Volus208/BioMeta/pcb/pcb.kicad_sch

## KiCad design pcb/pcb.kicad_sch (2023-11-06)

Schematic: pcb.kicad_sch

Parts:
D1, D2, D3, D4, D5, D6, D7, D8, D9, D10, D11, D12, D13, D14, D15, D16, D17, D18, D19, D20, D21, D22, D23, D24, D25, D26, D27, D28, D29, D30, D31, D32, D33, D34, D35, D36, D37, D38, D39, D40, D41, D42, D43, D44, D45, D46, D47, D48, D49, D50, D51, D52, D53, D54, D55, D56, D57, D58, D59, D60, D61, D62, D63, D64, D65, D66, D67, D68, D69, D70, D71, D72, D73, D74, D75, D76, D77, D78, D79, D80, D81, D82, D83, D84, D85, D86, D87, D88, D89, D90, D91, D92, D93, D94, D95, D96, D97, D98: D; D_SOD-123
FS1: FPM10A_fingerprint_sensor; solderpads_4
J1, J2: JST-S8B-XH-A-1; JST_XH_S8B-XH-A-1_1x08_P2.50mm_Horizontal
K1, K2, K3, K4, K5, K6, K7, K8, K9, K10, K11, K12, K14, K15, K16, K17, K18, K20, K21, K22, K23, K24, K26, K27, K28, K29, K30, K35, K36, K37, K38, K39, K40, K41, K42, K43, K44, K45, K46, K47, K48, K49, K50, K51, K52, K54, K55, K56, K57, K58, K59, K60, K61, K62, K63, K64, K66, K67, K68, K69, K70, K71, K72, K73, K74, K76, K77, K78, K80, K81, K82, K83, K84, K86, K87, K88, K89, K93, K94, K95, K96, K97: KEYSW; Mx_Alps_100
K13, K65, K91, K92: KEYSW; Mx_Alps_150
K19, K85: KEYSW; Mx_Alps_175
K25, K75: KEYSW; Mx_Alps_225
K31, K32, K33: KEYSW; Mx_Alps_125
K34, K90: KEYSW; Mx_Alps_312
K53, K79, K98: KEYSW; Mx_Alps_200
LED1, LED2, LED3, LED4, LED5, LED6, LED7, LED8, LED9, LED10, LED11, LED12, LED13, LED14, LED15, LED16, LED17, LED18, LED19, LED20, LED21, LED22, LED23, LED24, LED25, LED26, LED27, LED28, LED29, LED30, LED31, LED32, LED33, LED34, LED35, LED36, LED37, LED38, LED39, LED40, LED41, LED42, LED43, LED44, LED45, LED46, LED47, LED48, LED49, LED50, LED51, LED52, LED53, LED54, LED55, LED56, LED57, LED58, LED59, LED60, LED61, LED62, LED63, LED64, LED65, LED66, LED67, LED68, LED69, LED70, LED71, LED72, LED73, LED74, LED75, LED76, LED77, LED78, LED79, LED80, LED81, LED82, LED83, LED84, LED85, LED86, LED87, LED88, LED89, LED90, LED91, LED92, LED93, LED94, LED95, LED96, LED97, LED98: WS2812B; LED_WS2812B_PLCC4_2.0x2.0mm_P1.0mm
U1, U2: ProMicro

Connections:
GND: FS1.1 (GND), J1.1, J1.8, J2.1, J2.8, LED1.3 (VSS), LED2.3 (VSS), LED3.3 (VSS), LED4.3 (VSS), LED5.3 (VSS), LED6.3 (VSS), LED7.3 (VSS), LED8.3 (VSS), LED9.3 (VSS), LED10.3 (VSS), LED11.3 (VSS), LED12.3 (VSS), LED13.3 (VSS), LED14.3 (VSS), LED15.3 (VSS), LED16.3 (VSS), LED17.3 (VSS), LED18.3 (VSS), LED19.3 (VSS), LED20.3 (VSS), LED21.3 (VSS), LED22.3 (VSS), LED23.3 (VSS), LED24.3 (VSS), LED25.3 (VSS), LED26.3 (VSS), LED27.3 (VSS), LED28.3 (VSS), LED29.3 (VSS), LED30.3 (VSS), LED31.3 (VSS), LED32.3 (VSS), LED33.3 (VSS), LED34.3 (VSS), LED35.3 (VSS), LED36.3 (VSS), LED37.3 (VSS), LED38.3 (VSS), LED39.3 (VSS), LED40.3 (VSS), LED41.3 (VSS), LED42.3 (VSS), LED43.3 (VSS), LED44.3 (VSS), LED45.3 (VSS), LED46.3 (VSS), LED47.3 (VSS), LED48.3 (VSS), LED49.3 (VSS), LED50.3 (VSS), LED51.3 (VSS), LED52.3 (VSS), LED53.3 (VSS), LED54.3 (VSS), LED55.3 (VSS), LED56.3 (VSS), LED57.3 (VSS), LED58.3 (VSS), LED59.3 (VSS), LED60.3 (VSS), LED61.3 (VSS), LED62.3 (VSS), LED63.3 (VSS), LED64.3 (VSS), LED65.3 (VSS), LED66.3 (VSS), LED67.3 (VSS), LED68.3 (VSS), LED69.3 (VSS), LED70.3 (VSS), LED71.3 (VSS), LED72.3 (VSS), LED73.3 (VSS), LED74.3 (VSS), LED75.3 (VSS), LED76.3 (VSS), LED77.3 (VSS), LED78.3 (VSS), LED79.3 (VSS), LED80.3 (VSS), LED81.3 (VSS), LED82.3 (VSS), LED83.3 (VSS), LED84.3 (VSS), LED85.3 (VSS), LED86.3 (VSS), LED87.3 (VSS), LED88.3 (VSS), LED89.3 (VSS), LED90.3 (VSS), LED91.3 (VSS), LED92.3 (VSS), LED93.3 (VSS), LED94.3 (VSS), LED95.3 (VSS), LED96.3 (VSS), LED97.3 (VSS), LED98.3 (VSS), U1.3 (GND), U1.4 (GND), U1.23 (GND), U2.3 (GND), U2.4 (GND), U2.23 (GND)
unnamed: D1.1 (K), D2.1 (K), D3.1 (K), D4.1 (K), D5.1 (K), D6.1 (K), U1.18 (F6)
unnamed: D1.2 (A), K1.2
unnamed: D2.2 (A), K2.2
unnamed: D3.2 (A), K3.2
unnamed: D4.2 (A), K4.2
unnamed: D5.2 (A), K5.2
unnamed: D6.2 (A), K6.2
unnamed: D7.2 (A), K7.2
unnamed: D8.2 (A), K8.2
unnamed: D9.2 (A), K9.2
unnamed: D7.1 (K), D8.1 (K), D9.1 (K), D10.1 (K), D11.1 (K), D12.1 (K), U1.17 (F7)
unnamed: D10.2 (A), K10.2
unnamed: D11.2 (A), K11.2
unnamed: D12.2 (A), K12.2
unnamed: D13.1 (K), D14.1 (K), D15.1 (K), D16.1 (K), D17.1 (K), D18.1 (K), U1.16 (B1)
unnamed: D13.2 (A), K13.2
unnamed: D14.2 (A), K14.2
unnamed: D15.2 (A), K15.2
unnamed: D16.2 (A), K16.2
unnamed: D17.2 (A), K17.2
unnamed: D18.2 (A), K18.2
unnamed: D19.1 (K), D20.1 (K), D21.1 (K), D22.1 (K), D23.1 (K), D24.1 (K), U1.15 (B3)
unnamed: D19.2 (A), K19.2
unnamed: D20.2 (A), K20.2
unnamed: D21.2 (A), K21.2
unnamed: D22.2 (A), K22.2
unnamed: D23.2 (A), K23.2
unnamed: D24.2 (A), K24.2
unnamed: D25.1 (K), D26.1 (K), D27.1 (K), D28.1 (K), D29.1 (K), D30.1 (K), U1.14 (B2)
unnamed: D25.2 (A), K25.2
unnamed: D26.2 (A), K26.2
unnamed: D27.2 (A), K27.2
unnamed: D28.2 (A), K28.2
unnamed: D29.2 (A), K29.2
unnamed: D30.2 (A), K30.2
unnamed: D31.1 (K), D32.1 (K), D33.1 (K), D34.1 (K), U1.13 (B6)
unnamed: D31.2 (A), K31.2
unnamed: D32.2 (A), K32.2
unnamed: D33.2 (A), K33.2
unnamed: D34.2 (A), K34.2
unnamed: D35.1 (K), D37.1 (K), D39.1 (K), D40.1 (K), D41.1 (K), D42.1 (K), D43.1 (K), D45.1 (K), U2.7 (D4)
unnamed: D35.2 (A), K35.2
unnamed: D36.1 (K), D38.1 (K), D44.1 (K), D50.1 (K), D52.1 (K), D53.1 (K), D54.1 (K), D57.1 (K), U2.8 (C6)
unnamed: D36.2 (A), K36.2
unnamed: D37.2 (A), K37.2
unnamed: D38.2 (A), K38.2
unnamed: D39.2 (A), K39.2
unnamed: D40.2 (A), K40.2
unnamed: D41.2 (A), K41.2
unnamed: D42.2 (A), K42.2
unnamed: D43.2 (A), K43.2
unnamed: D44.2 (A), K44.2
unnamed: D45.2 (A), K45.2
unnamed: D46.1 (K), D48.1 (K), D51.1 (K), D55.1 (K), D63.1 (K), D64.1 (K), D66.1 (K), D68.1 (K), U2.9 (D7)
unnamed: D46.2 (A), K46.2
unnamed: D47.1 (K), D49.1 (K), D56.1 (K), D61.1 (K), D65.1 (K), D74.1 (K), D76.1 (K), D79.1 (K), U2.10 (E6)
unnamed: D47.2 (A), K47.2
unnamed: D48.2 (A), K48.2
unnamed: D49.2 (A), K49.2
unnamed: D50.2 (A), K50.2
unnamed: D51.2 (A), K51.2
unnamed: D52.2 (A), K52.2
unnamed: D53.2 (A), K53.2
unnamed: D54.2 (A), K54.2
unnamed: D55.2 (A), K55.2
unnamed: D56.2 (A), K56.2
unnamed: D57.2 (A), K57.2
unnamed: D58.1 (K), D59.1 (K), D62.1 (K), D67.1 (K), D73.1 (K), D75.1 (K), D78.1 (K), D87.1 (K), U2.11 (B4)
unnamed: D58.2 (A), K58.2
unnamed: D59.2 (A), K59.2
unnamed: D60.1 (K), D69.1 (K), D71.1 (K), D77.1 (K), D83.1 (K), D86.1 (K), D89.1 (K), D93.1 (K), U2.12 (B5)
unnamed: D60.2 (A), K60.2
unnamed: D61.2 (A), K61.2
unnamed: D62.2 (A), K62.2
unnamed: D63.2 (A), K63.2
unnamed: D64.2 (A), K64.2
unnamed: D65.2 (A), K65.2
unnamed: D66.2 (A), K66.2
unnamed: D67.2 (A), K67.2
unnamed: D68.2 (A), K68.2
unnamed: D69.2 (A), K69.2
unnamed: D70.1 (K), D72.1 (K), D80.1 (K), D84.1 (K), D85.1 (K), D88.1 (K), D94.1 (K), D98.1 (K), U2.13 (B6)
unnamed: D70.2 (A), K70.2
unnamed: D71.2 (A), K71.2
unnamed: D72.2 (A), K72.2
unnamed: D73.2 (A), K73.2
unnamed: D74.2 (A), K74.2
unnamed: D75.2 (A), K75.2
unnamed: D76.2 (A), K76.2
unnamed: D77.2 (A), K77.2
unnamed: D78.2 (A), K78.2
unnamed: D79.2 (A), K79.2
unnamed: D80.2 (A), K80.2
unnamed: D81.1 (K), D82.1 (K), D90.1 (K), D91.1 (K), D92.1 (K), D95.1 (K), D96.1 (K), D97.1 (K), U2.14 (B2)
unnamed: D81.2 (A), K81.2
unnamed: D82.2 (A), K82.2
unnamed: D83.2 (A), K83.2
unnamed: D84.2 (A), K84.2
unnamed: D85.2 (A), K85.2
unnamed: D86.2 (A), K86.2
unnamed: D87.2 (A), K87.2
unnamed: D88.2 (A), K88.2
unnamed: D89.2 (A), K89.2
unnamed: D90.2 (A), K90.2
unnamed: D91.2 (A), K91.2
unnamed: D92.2 (A), K92.2
unnamed: D93.2 (A), K93.2
unnamed: D94.2 (A), K94.2
unnamed: D95.2 (A), K95.2
unnamed: D96.2 (A), K96.2
unnamed: D97.2 (A), K97.2
unnamed: D98.2 (A), K98.2
unnamed: FS1.2 (RX), U1.1 (TX)
unnamed: FS1.3 (TX), U1.2 (RX)
unnamed: FS1.4 (VIN), J1.2, J1.7, LED1.1 (VDD), LED2.1 (VDD), LED3.1 (VDD), LED4.1 (VDD), LED5.1 (VDD), LED6.1 (VDD), LED7.1 (VDD), LED8.1 (VDD), LED9.1 (VDD), LED10.1 (VDD), LED11.1 (VDD), LED12.1 (VDD), LED13.1 (VDD), LED14.1 (VDD), LED15.1 (VDD), LED16.1 (VDD), LED17.1 (VDD), LED18.1 (VDD), LED19.1 (VDD), LED20.1 (VDD), LED21.1 (VDD), LED22.1 (VDD), LED23.1 (VDD), LED24.1 (VDD), LED25.1 (VDD), LED26.1 (VDD), LED27.1 (VDD), LED28.1 (VDD), LED29.1 (VDD), LED30.1 (VDD), LED31.1 (VDD), LED32.1 (VDD), LED33.1 (VDD), LED34.1 (VDD), U1.21 (VCC)
unnamed: J1.3, J1.4, LED34.2 (DOUT)
unnamed: J1.5, U1.6 (SCL)
unnamed: J1.6, U1.5 (SDA)
unnamed: J2.2, J2.7, LED35.1 (VDD), LED36.1 (VDD), LED37.1 (VDD), LED38.1 (VDD), LED39.1 (VDD), LED40.1 (VDD), LED41.1 (VDD), LED42.1 (VDD), LED43.1 (VDD), LED44.1 (VDD), LED45.1 (VDD), LED46.1 (VDD), LED47.1 (VDD), LED48.1 (VDD), LED49.1 (VDD), LED50.1 (VDD), LED51.1 (VDD), LED52.1 (VDD), LED53.1 (VDD), LED54.1 (VDD), LED55.1 (VDD), LED56.1 (VDD), LED57.1 (VDD), LED58.1 (VDD), LED59.1 (VDD), LED60.1 (VDD), LED61.1 (VDD), LED62.1 (VDD), LED63.1 (VDD), LED64.1 (VDD), LED65.1 (VDD), LED66.1 (VDD), LED67.1 (VDD), LED68.1 (VDD), LED69.1 (VDD), LED70.1 (VDD), LED71.1 (VDD), LED72.1 (VDD), LED73.1 (VDD), LED74.1 (VDD), LED75.1 (VDD), LED76.1 (VDD), LED77.1 (VDD), LED78.1 (VDD), LED79.1 (VDD), LED80.1 (VDD), LED81.1 (VDD), LED82.1 (VDD), LED83.1 (VDD), LED84.1 (VDD), LED85.1 (VDD), LED86.1 (VDD), LED87.1 (VDD), LED88.1 (VDD), LED89.1 (VDD), LED90.1 (VDD), LED91.1 (VDD), LED92.1 (VDD), LED93.1 (VDD), LED94.1 (VDD), LED95.1 (VDD), LED96.1 (VDD), LED97.1 (VDD), LED98.1 (VDD), U2.21 (VCC)
unnamed: J2.3, J2.4, LED45.4 (DIN)
unnamed: J2.5, U2.6 (SCL)
unnamed: J2.6, U2.5 (SDA)
unnamed: K1.1, K7.1, K13.1, K19.1, K25.1, K31.1, U1.7 (D4)
unnamed: K4.1, K10.1, K16.1, K22.1, K28.1, K34.1, U1.10 (E6)
unnamed: K5.1, K11.1, K17.1, K23.1, K29.1, U1.11 (B4)
unnamed: K6.1, K12.1, K18.1, K24.1, K30.1, U1.12 (B5)
unnamed: K2.1, K8.1, K14.1, K20.1, K26.1, K32.1, U1.8 (C6)
unnamed: K3.1, K9.1, K15.1, K21.1, K27.1, K33.1, U1.9 (D7)
unnamed: K35.1, K36.1, K46.1, K47.1, K58.1, K69.1, K80.1, K90.1, U2.15 (B3)
unnamed: K37.1, K38.1, K48.1, K49.1, K59.1, K60.1, K70.1, K81.1, U2.16 (B1)
unnamed: K39.1, K50.1, K51.1, K61.1, K62.1, K71.1, K72.1, K82.1, U2.17 (F7)
unnamed: K40.1, K52.1, K63.1, K73.1, K74.1, K83.1, K84.1, K91.1, U2.18 (F6)
unnamed: K41.1, K53.1, K64.1, K65.1, K75.1, K85.1, K86.1, K92.1, U2.19 (F5)
unnamed: K42.1, K54.1, K66.1, K76.1, K87.1, K93.1, K94.1, K95.1, U2.20 (F4)
unnamed: K43.1, K44.1, K55.1, K56.1, K67.1, K77.1, K88.1, K96.1, U2.1 (TX)
unnamed: K45.1, K57.1, K68.1, K78.1, K79.1, K89.1, K97.1, K98.1, U2.2 (RX)
unnamed: LED1.2 (DOUT), LED2.4 (DIN)
unnamed: LED1.4 (DIN), U1.19 (F5)
unnamed: LED2.2 (DOUT), LED3.4 (DIN)
unnamed: LED3.2 (DOUT), LED4.4 (DIN)
unnamed: LED4.2 (DOUT), LED5.4 (DIN)
unnamed: LED5.2 (DOUT), LED6.4 (DIN)
unnamed: LED6.2 (DOUT), LED7.4 (DIN)
unnamed: LED7.2 (DOUT), LED8.4 (DIN)
unnamed: LED8.2 (DOUT), LED9.4 (DIN)
unnamed: LED10.2 (DOUT), LED11.4 (DIN)
unnamed: LED9.2 (DOUT), LED10.4 (DIN)
unnamed: LED11.2 (DOUT), LED12.4 (DIN)
unnamed: LED12.2 (DOUT), LED13.4 (DIN)
unnamed: LED13.2 (DOUT), LED14.4 (DIN)
unnamed: LED14.2 (DOUT), LED15.4 (DIN)
unnamed: LED15.2 (DOUT), LED16.4 (DIN)
unnamed: LED16.2 (DOUT), LED17.4 (DIN)
unnamed: LED17.2 (DOUT), LED18.4 (DIN)
unnamed: LED18.2 (DOUT), LED19.4 (DIN)
unnamed: LED19.2 (DOUT), LED20.4 (DIN)
unnamed: LED20.2 (DOUT), LED21.4 (DIN)
unnamed: LED21.2 (DOUT), LED22.4 (DIN)
unnamed: LED22.2 (DOUT), LED23.4 (DIN)
unnamed: LED23.2 (DOUT), LED24.4 (DIN)
unnamed: LED24.2 (DOUT), LED25.4 (DIN)
unnamed: LED25.2 (DOUT), LED26.4 (DIN)
unnamed: LED26.2 (DOUT), LED27.4 (DIN)
unnamed: LED27.2 (DOUT), LED28.4 (DIN)
unnamed: LED28.2 (DOUT), LED29.4 (DIN)
unnamed: LED29.2 (DOUT), LED30.4 (DIN)
unnamed: LED30.2 (DOUT), LED31.4 (DIN)
unnamed: LED31.2 (DOUT), LED32.4 (DIN)
unnamed: LED32.2 (DOUT), LED33.4 (DIN)
unnamed: LED33.2 (DOUT), LED34.4 (DIN)
unnamed: LED35.2 (DOUT), LED46.4 (DIN)
unnamed: LED35.4 (DIN), LED36.2 (DOUT)
unnamed: LED36.4 (DIN), LED37.2 (DOUT)
unnamed: LED37.4 (DIN), LED38.2 (DOUT)
unnamed: LED38.4 (DIN), LED39.2 (DOUT)
unnamed: LED39.4 (DIN), LED40.2 (DOUT)
unnamed: LED40.4 (DIN), LED41.2 (DOUT)
unnamed: LED41.4 (DIN), LED42.2 (DOUT)
unnamed: LED42.4 (DIN), LED43.2 (DOUT)
unnamed: LED43.4 (DIN), LED44.2 (DOUT)
unnamed: LED44.4 (DIN), LED45.2 (DOUT)
unnamed: LED46.2 (DOUT), LED47.4 (DIN)
unnamed: LED47.2 (DOUT), LED48.4 (DIN)
unnamed: LED48.2 (DOUT), LED49.4 (DIN)
unnamed: LED49.2 (DOUT), LED50.4 (DIN)
unnamed: LED50.2 (DOUT), LED51.4 (DIN)
unnamed: LED51.2 (DOUT), LED52.4 (DIN)
unnamed: LED52.2 (DOUT), LED53.4 (DIN)
unnamed: LED53.2 (DOUT), LED54.4 (DIN)
unnamed: LED54.2 (DOUT), LED55.4 (DIN)
unnamed: LED55.2 (DOUT), LED56.4 (DIN)
unnamed: LED56.2 (DOUT), LED57.4 (DIN)
unnamed: LED57.2 (DOUT), LED68.4 (DIN)
unnamed: LED58.2 (DOUT), LED69.4 (DIN)
unnamed: LED58.4 (DIN), LED59.2 (DOUT)
unnamed: LED59.4 (DIN), LED60.2 (DOUT)
unnamed: LED60.4 (DIN), LED61.2 (DOUT)
unnamed: LED61.4 (DIN), LED62.2 (DOUT)
unnamed: LED62.4 (DIN), LED63.2 (DOUT)
unnamed: LED63.4 (DIN), LED64.2 (DOUT)
unnamed: LED64.4 (DIN), LED65.2 (DOUT)
unnamed: LED65.4 (DIN), LED66.2 (DOUT)
unnamed: LED66.4 (DIN), LED67.2 (DOUT)
unnamed: LED67.4 (DIN), LED68.2 (DOUT)
unnamed: LED69.2 (DOUT), LED70.4 (DIN)
unnamed: LED70.2 (DOUT), LED71.4 (DIN)
unnamed: LED71.2 (DOUT), LED72.4 (DIN)
unnamed: LED72.2 (DOUT), LED73.4 (DIN)
unnamed: LED73.2 (DOUT), LED74.4 (DIN)
unnamed: LED74.2 (DOUT), LED75.4 (DIN)
unnamed: LED75.2 (DOUT), LED76.4 (DIN)
unnamed: LED76.2 (DOUT), LED77.4 (DIN)
unnamed: LED77.2 (DOUT), LED78.4 (DIN)
unnamed: LED78.2 (DOUT), LED79.4 (DIN)
unnamed: LED79.2 (DOUT), LED89.4 (DIN)
unnamed: LED80.2 (DOUT), LED90.4 (DIN)
unnamed: LED80.4 (DIN), LED81.2 (DOUT)
unnamed: LED81.4 (DIN), LED82.2 (DOUT)
unnamed: LED82.4 (DIN), LED83.2 (DOUT)
unnamed: LED83.4 (DIN), LED84.2 (DOUT)
unnamed: LED84.4 (DIN), LED85.2 (DOUT)
unnamed: LED85.4 (DIN), LED86.2 (DOUT)
unnamed: LED86.4 (DIN), LED87.2 (DOUT)
unnamed: LED87.4 (DIN), LED88.2 (DOUT)
unnamed: LED88.4 (DIN), LED89.2 (DOUT)
unnamed: LED90.2 (DOUT), LED91.4 (DIN)
unnamed: LED91.2 (DOUT), LED92.4 (DIN)
unnamed: LED92.2 (DOUT), LED93.4 (DIN)
unnamed: LED93.2 (DOUT), LED94.4 (DIN)
unnamed: LED94.2 (DOUT), LED95.4 (DIN)
unnamed: LED95.2 (DOUT), LED96.4 (DIN)
unnamed: LED96.2 (DOUT), LED97.4 (DIN)
unnamed: LED97.2 (DOUT), LED98.4 (DIN)
